bcrist/16717a/3d/pqfp208.step

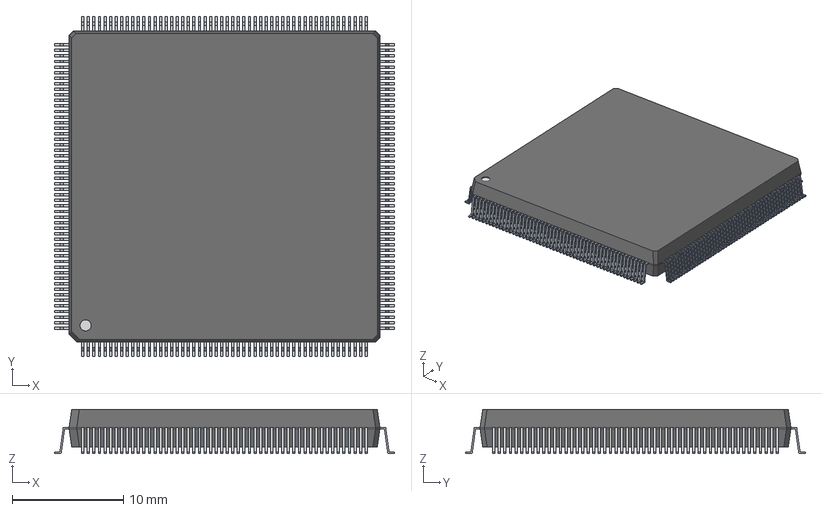
[picture p31: CAD file, 2025-01-23]
3d/pqfp208.step
30.6 x 30.6 x 4.00 mm
