bcrist/16717a/3d/oscillator_dip14.step

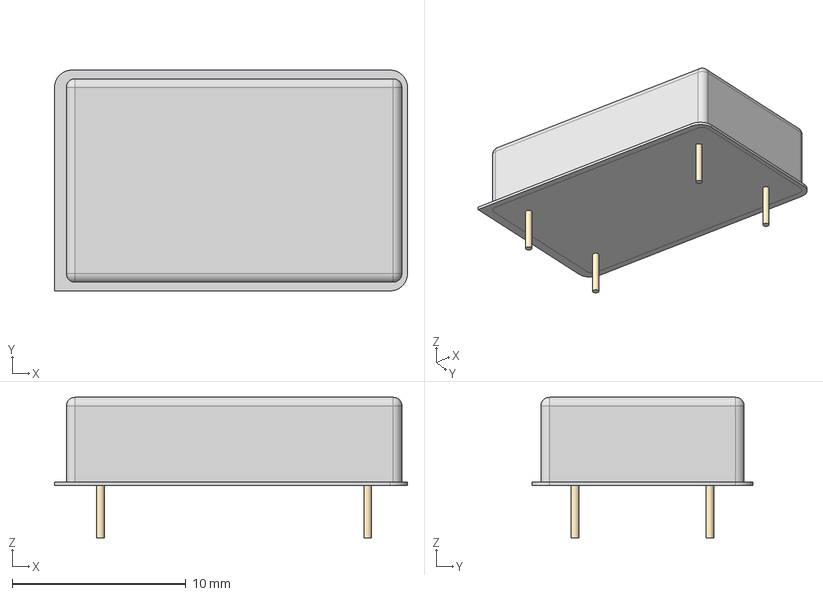
[picture p32: CAD file, 2025-01-23]
3d/oscillator_dip14.step
20.3 x 12.7 x 8.08 mm
