bcrist/16717a/3d/fb_axial.step

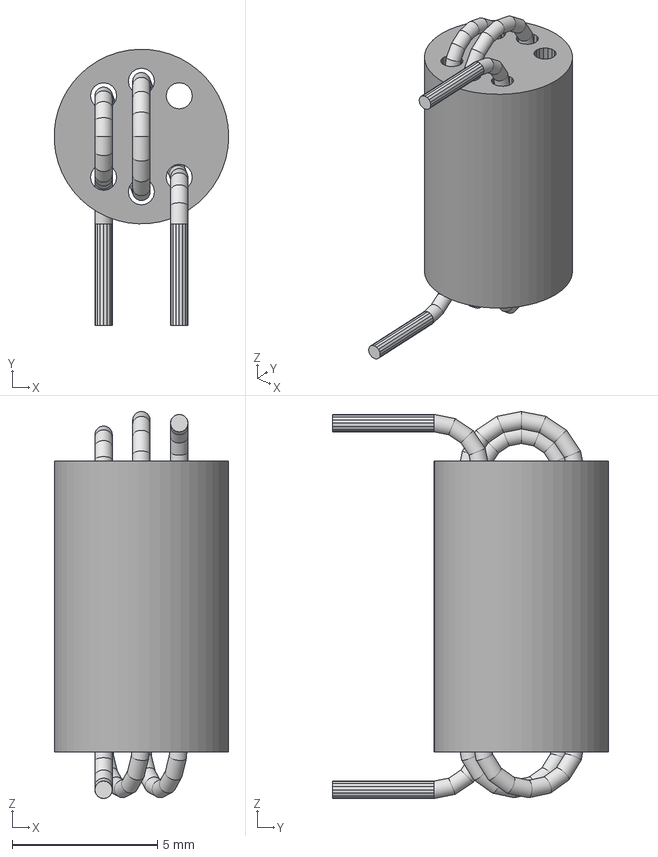
[picture p33: CAD file, 2025-01-23]
3d/fb_axial.step
5.99 x 9.50 x 13.3 mm
prism006
prism007
prism008
prism009
prism010
PrismaticToroid
PrismaticToroid001
PrismaticToroid002
PrismaticToroid003
prism011
PrismaticToroid004
prism012
prism013
PrismaticToroid005
prism014
