bcrist/16717a/3d/ssop14.step

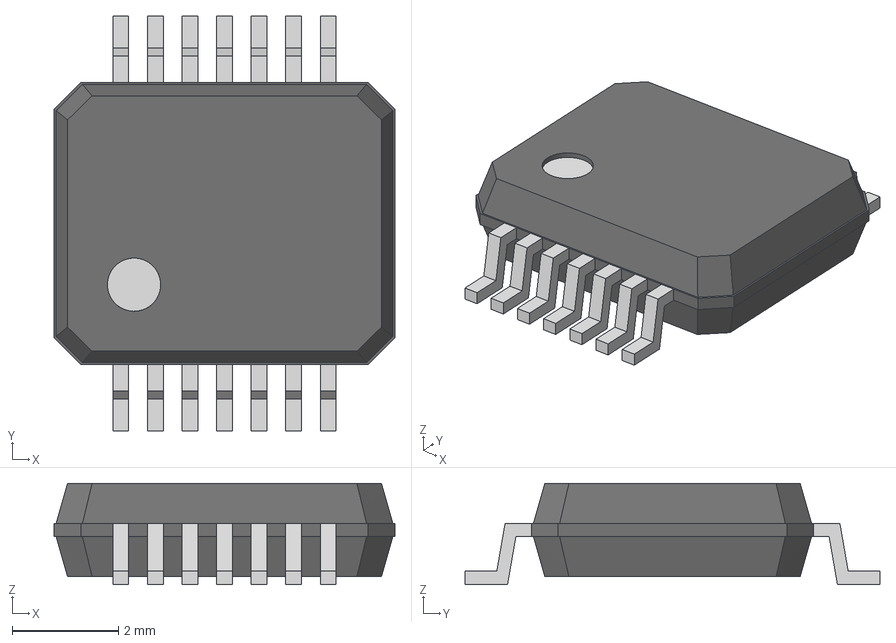
[picture p34: CAD file, 2025-01-23]
3d/ssop14.step
6.40 x 7.80 x 1.90 mm
