bcrist/16717a/3d/to263-5.step

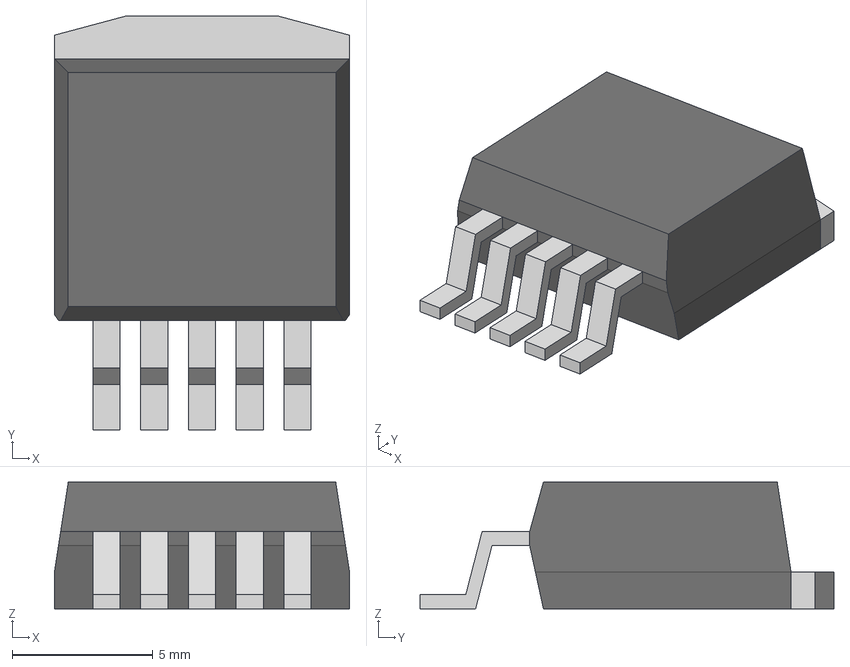
[picture p35: CAD file, 2025-01-23]
3d/to263-5.step
10.5 x 14.7 x 4.50 mm
