bcrist/16717a/3d/pod_connector.step

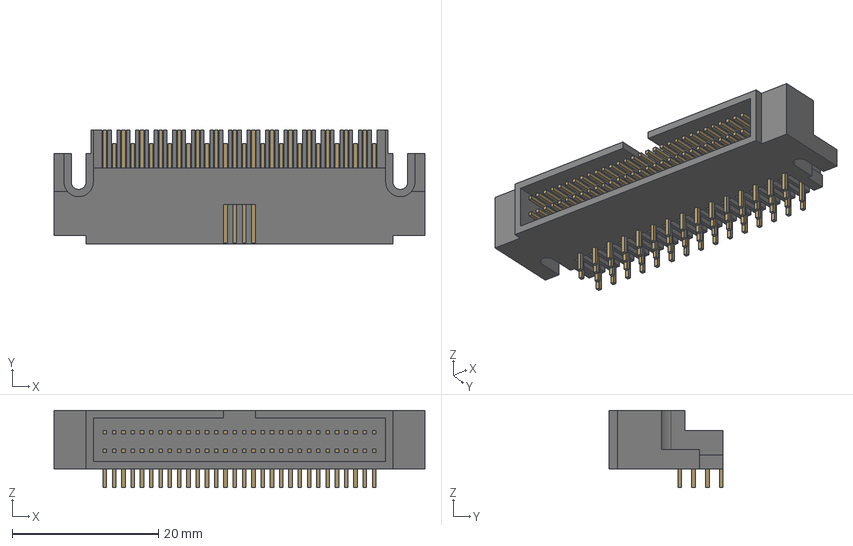
[picture p36: CAD file, 2025-01-23]
3d/pod_connector.step
50.8 x 15.7 x 10.5 mm
