bcrist/16717a/3d/to263heatsink.step

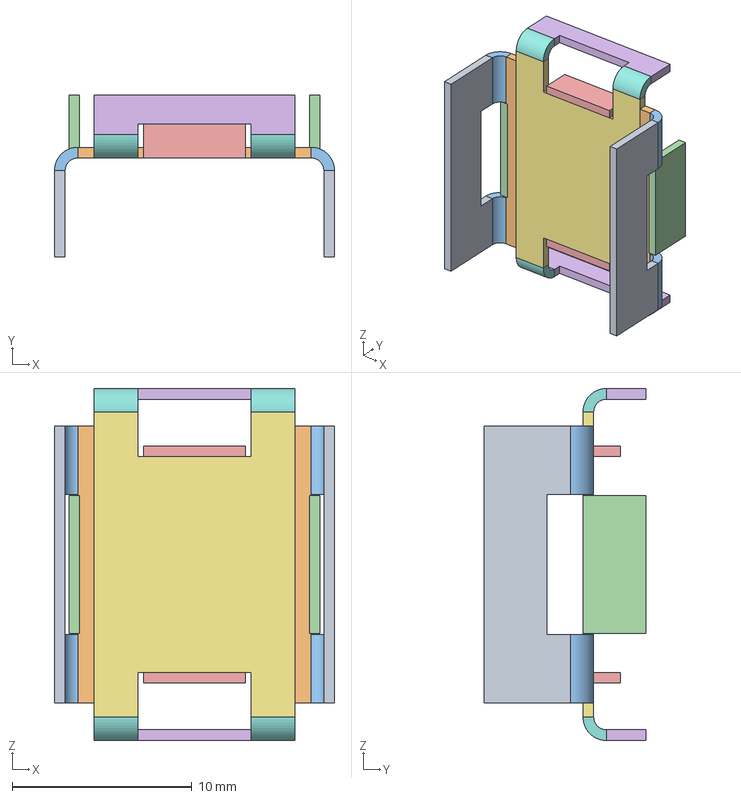
[picture p37: CAD file, 2025-01-23]
3d/to263heatsink.step
15.6 x 9.00 x 19.6 mm
