bcrist/16717a/3d/tqfp144.step

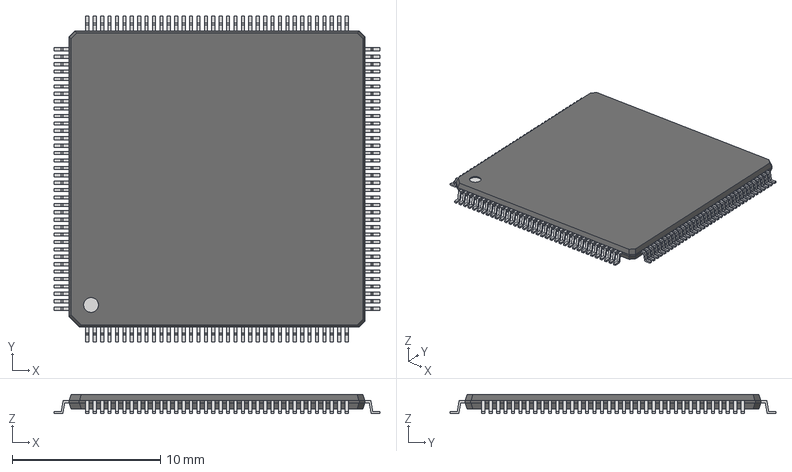
[picture p38: CAD file, 2025-01-23]
3d/tqfp144.step
22.0 x 22.0 x 1.30 mm
