bcrist/16717a/3d/soic20w.step

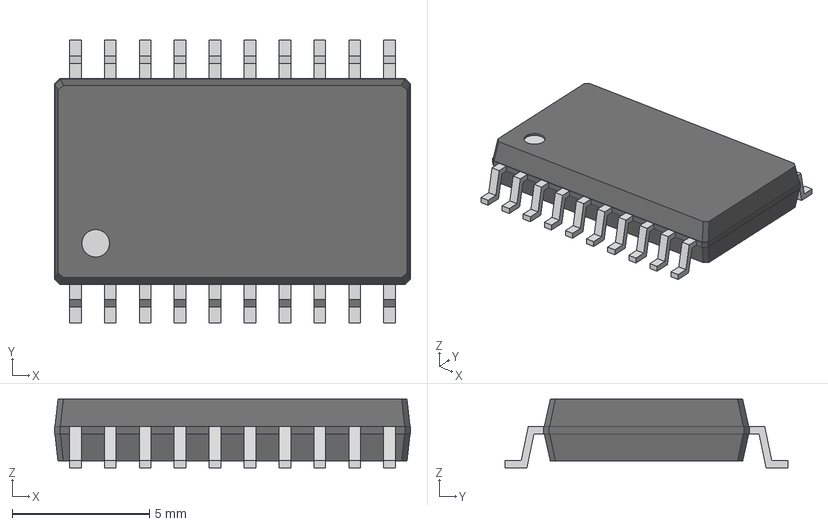
[picture p39: CAD file, 2025-01-23]
3d/soic20w.step
12.9 x 10.3 x 2.50 mm
