bcrist/16717a/3d/qfp44.step

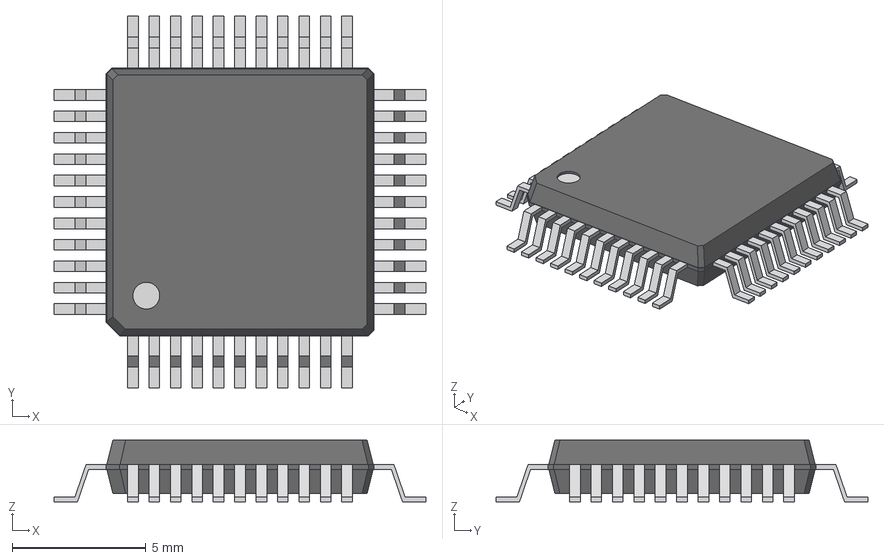
[picture p40: CAD file, 2025-01-23]
3d/qfp44.step
13.9 x 13.9 x 2.30 mm
