bcrist/16717a/3d/qfp52.step

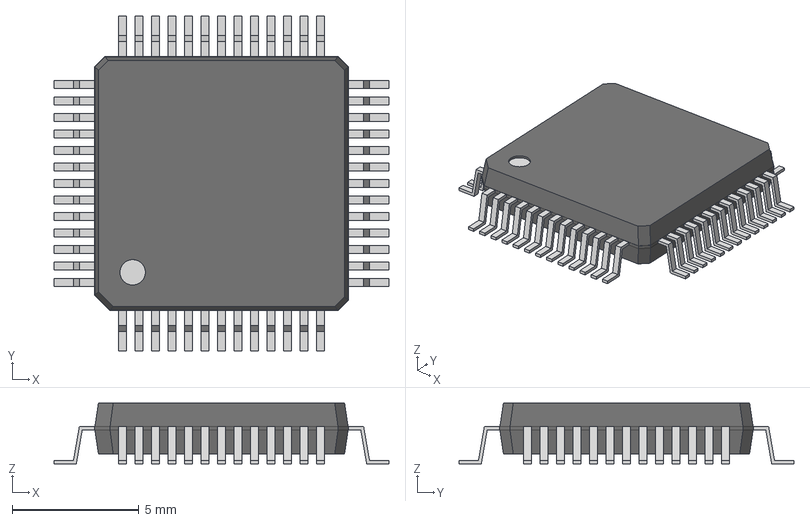
[picture p41: CAD file, 2025-01-23]
3d/qfp52.step
13.2 x 13.2 x 2.40 mm
