bcrist/16717a/3d/soic16.step

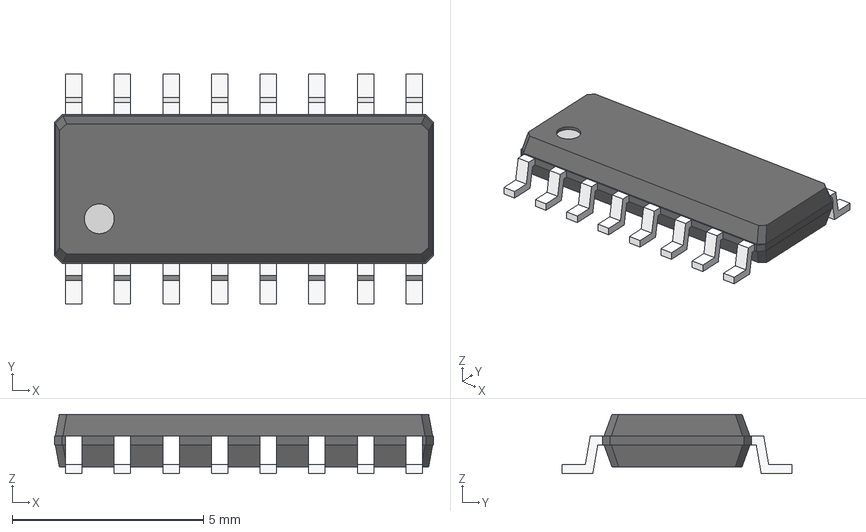
[picture p42: CAD file, 2025-01-23]
3d/soic16.step
9.90 x 6.00 x 1.55 mm
