bcrist/16717a/3d/soic16wr.step

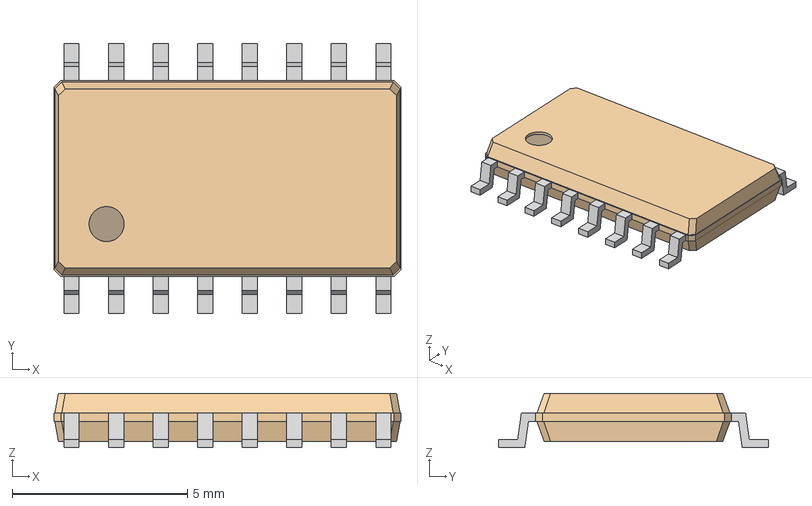
[picture p43: CAD file, 2025-01-23]
3d/soic16wr.step
9.90 x 7.70 x 1.55 mm
