bcrist/16717a/3d/AMP_1-534204-4.step

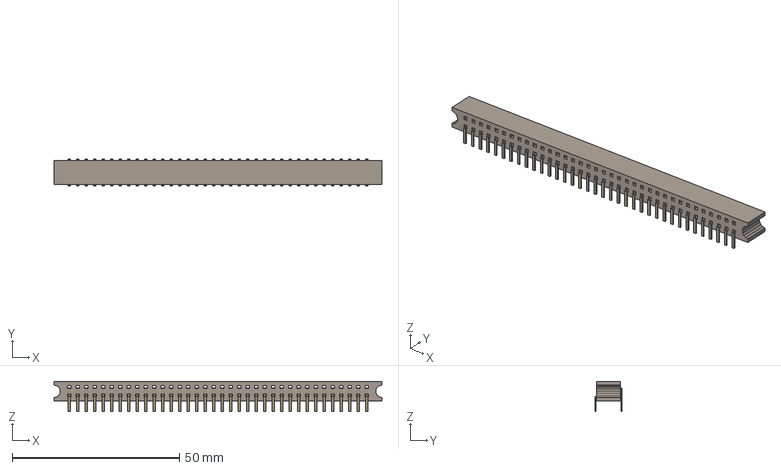
[picture p44: CAD file, 2025-01-23]
3d/AMP_1-534204-4.step
98.0 x 8.17 x 9.00 mm
